magore/allsky-rpi-hq-camera-enclosure/images/BOTTOM-COVER-AND-WEATHER-SENSOR/ALLSKY-CAMERA-BOTTOM-VIEW-CLOSEUP.jpg

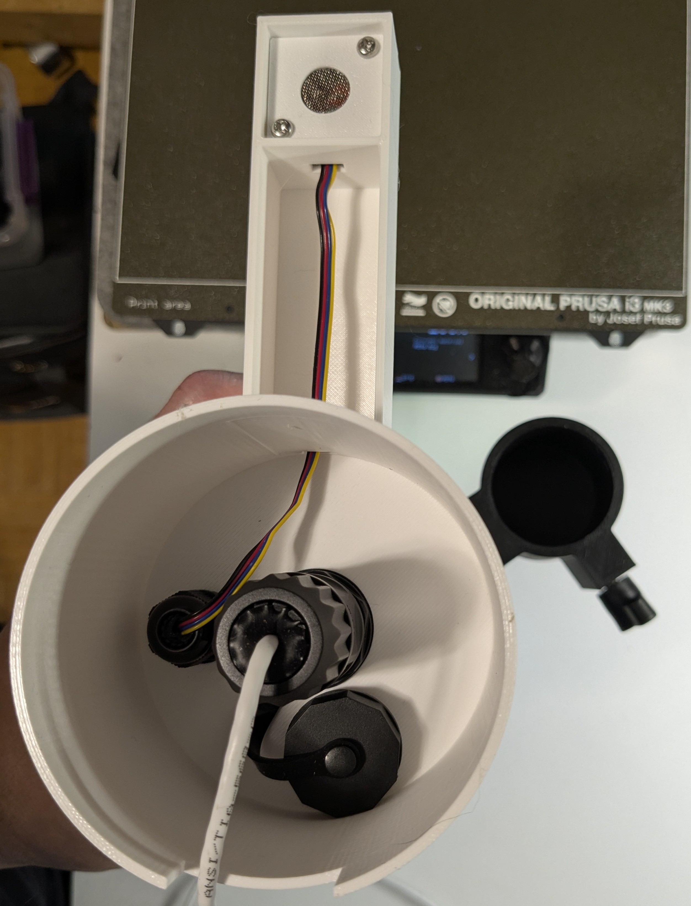
images/BOTTOM-COVER-AND-WEATHER-SENSOR/ALLSKY-CAMERA-BOTTOM-VIEW-CLOSEUP.jpg
