magore/allsky-rpi-hq-camera-enclosure/images/BOTTOM-COVER-AND-WEATHER-SENSOR/WEATHER-SENSOR-AND-COVER.jpg

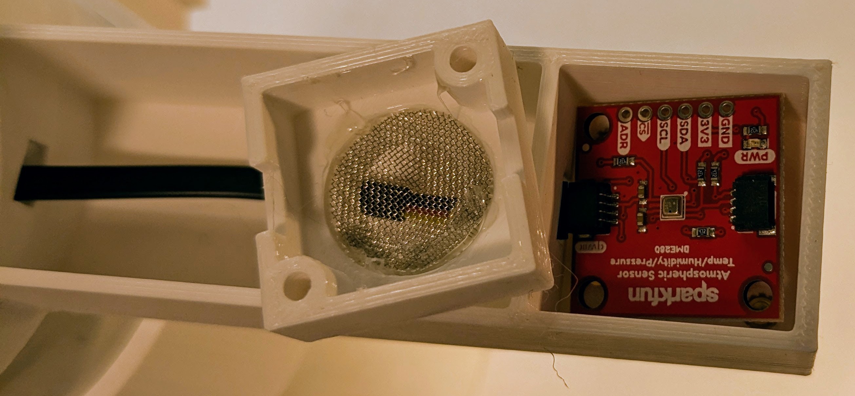
images/BOTTOM-COVER-AND-WEATHER-SENSOR/WEATHER-SENSOR-AND-COVER.jpg
