magore/allsky-rpi-hq-camera-enclosure/images/BOTTOM-COVER-AND-WEATHER-SENSOR/WEATHER-SENSOR-COVER-AND-SCREEN.jpg

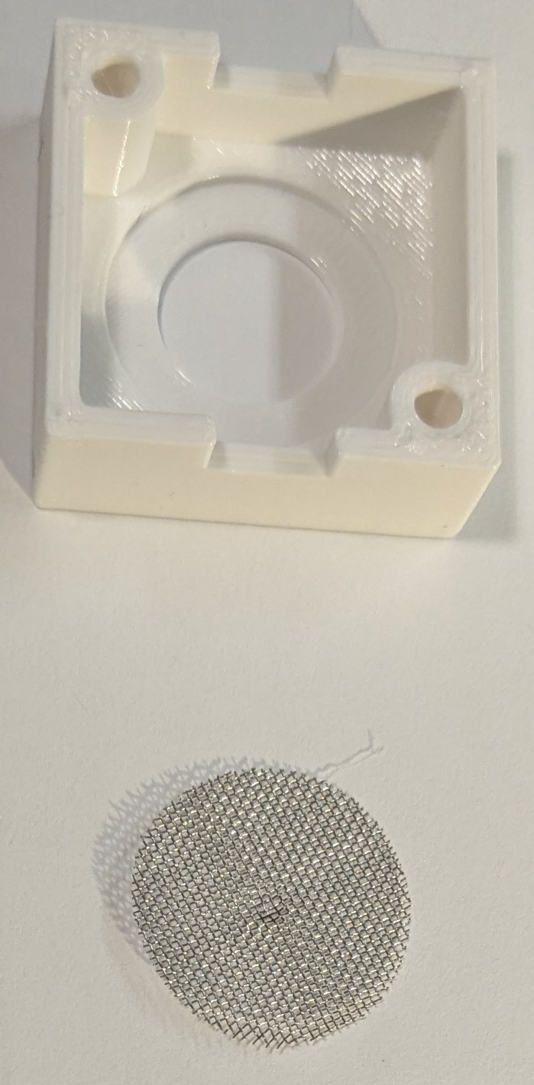
images/BOTTOM-COVER-AND-WEATHER-SENSOR/WEATHER-SENSOR-COVER-AND-SCREEN.jpg
