magore/allsky-rpi-hq-camera-enclosure/images/enclosure.jpg

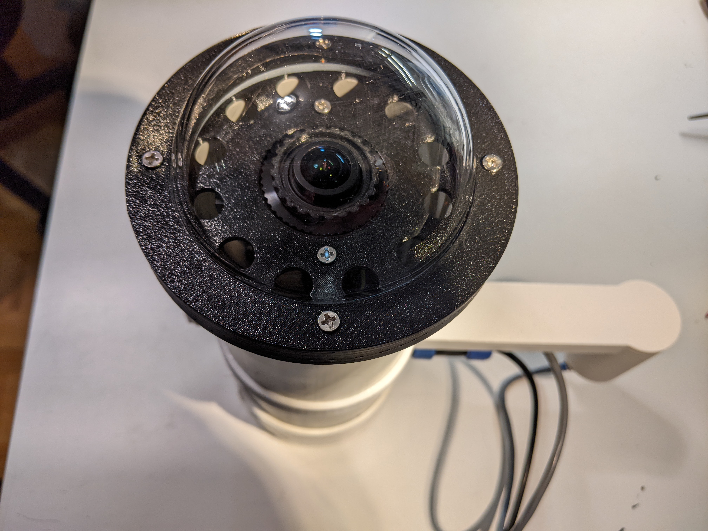
images/enclosure.jpg
