magore/allsky-rpi-hq-camera-enclosure/images/HEAT-SET-INSERT-INSTALLATION/HEAT-SET-INSERT-REQUIRMENTS-FOR-THIS-PROJECTS-CAD-DESIGN.jpg

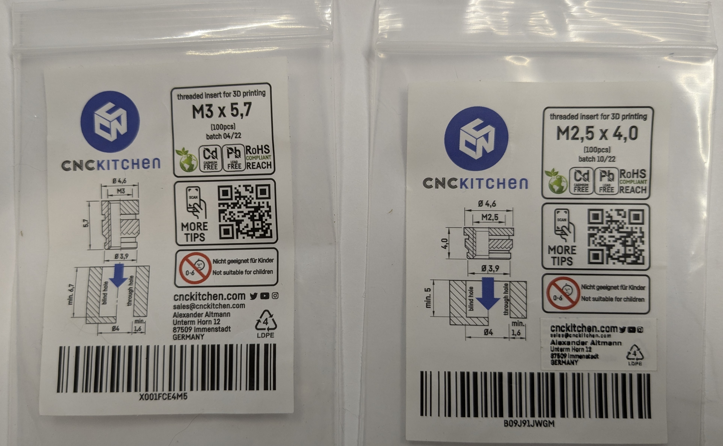
images/HEAT-SET-INSERT-INSTALLATION/HEAT-SET-INSERT-REQUIRMENTS-FOR-THIS-PROJECTS-CAD-DESIGN.jpg
