magore/allsky-rpi-hq-camera-enclosure/images/MAGNETIC-FOCUS/MAGNETIC-FOCUS-ADJUSTMENT.jpg

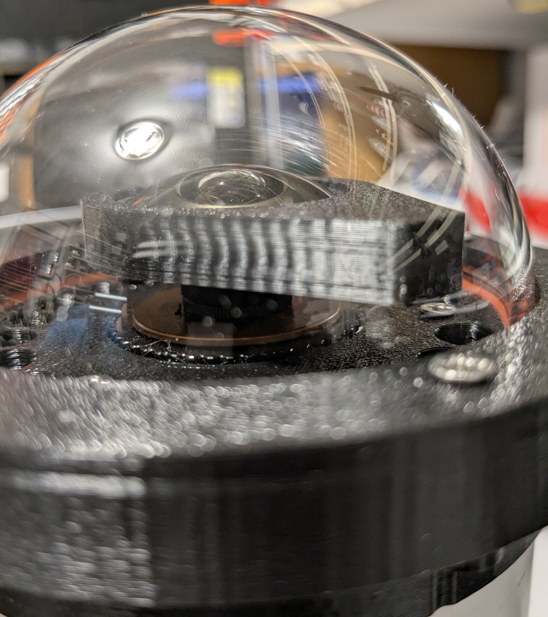
images/MAGNETIC-FOCUS/MAGNETIC-FOCUS-ADJUSTMENT.jpg
