magore/allsky-rpi-hq-camera-enclosure/images/MOUNTING/ALLSKY-POLLTOP-MOUNT-ADAPTER.jpg

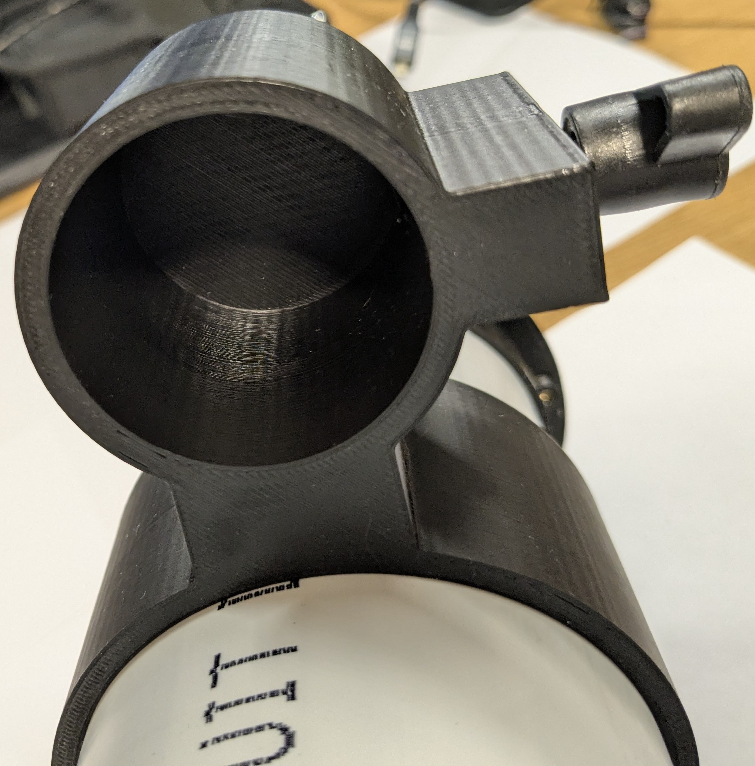
images/MOUNTING/ALLSKY-POLLTOP-MOUNT-ADAPTER.jpg
