magore/allsky-rpi-hq-camera-enclosure/images/O-RING-INSTALLATION/ALLSKY-CAMERA-O-RING-VERSION-OPTICAL-COVER-REMOVED.jpg

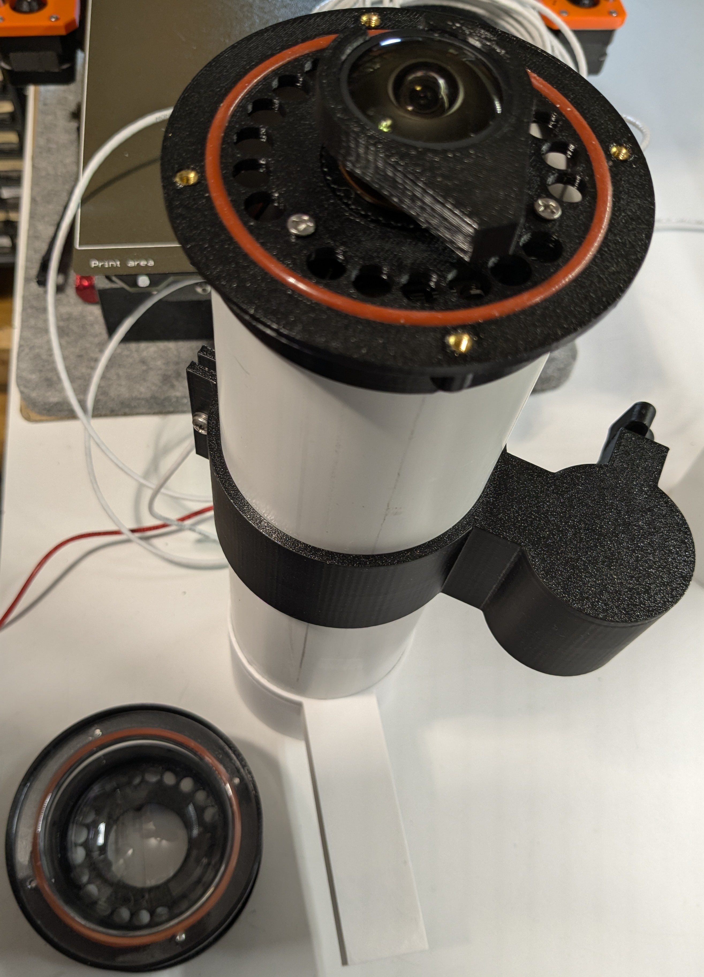
images/O-RING-INSTALLATION/ALLSKY-CAMERA-O-RING-VERSION-OPTICAL-COVER-REMOVED.jpg
