magore/allsky-rpi-hq-camera-enclosure/images/O-RING-INSTALLATION/TOP-COVER-OPTICAL-DOME-O-RINGs.jpg

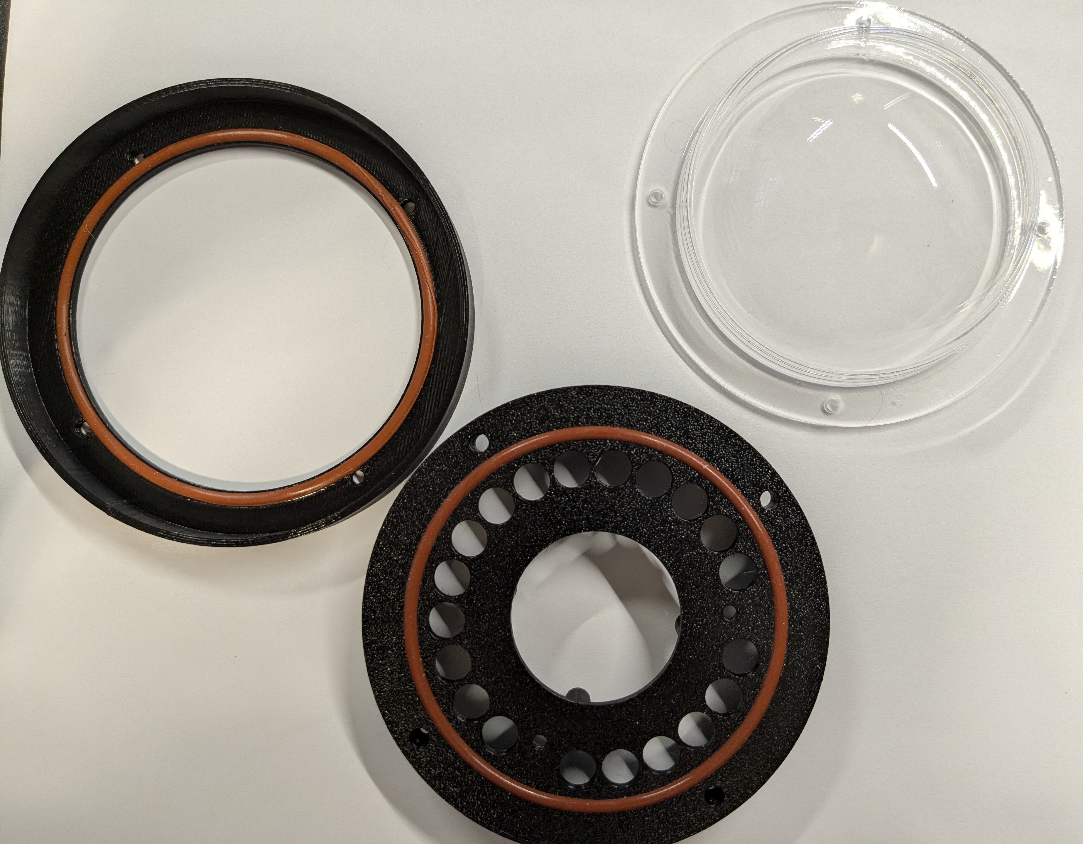
images/O-RING-INSTALLATION/TOP-COVER-OPTICAL-DOME-O-RINGs.jpg
