magore/allsky-rpi-hq-camera-enclosure/images/WEATHER-SENSOR-AND-BOTTOP-COVER-TOP-INSIDE-VIEW.jpg

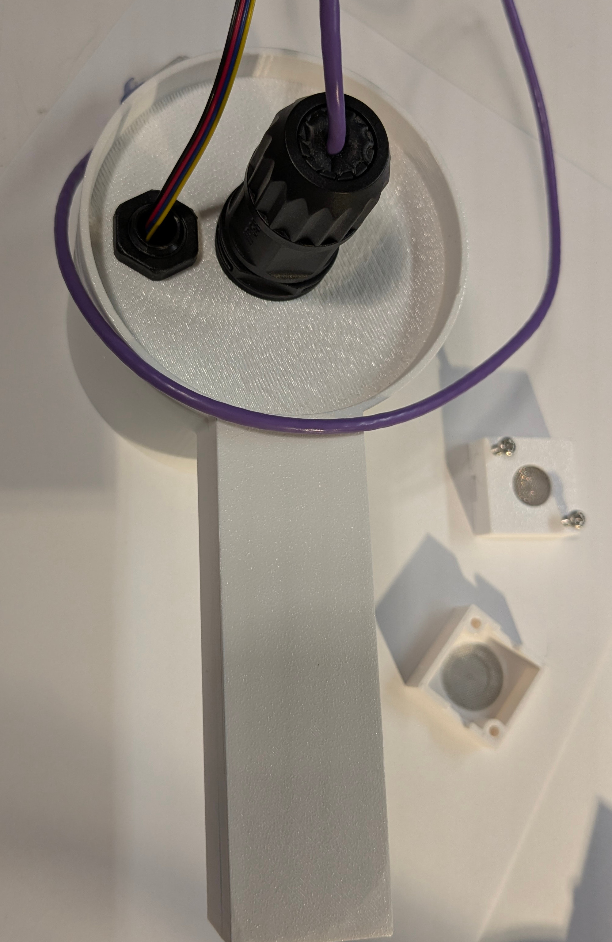
images/WEATHER-SENSOR-AND-BOTTOP-COVER-TOP-INSIDE-VIEW.jpg
