magore/allsky-rpi-hq-camera-enclosure/images/BOTTOM-COVER-AND-WEATHER-SENSOR/BOTTOM-VIEW-WEATHER-SENSOR-INSIDE-ASSEMBLY-VIEW.jpg

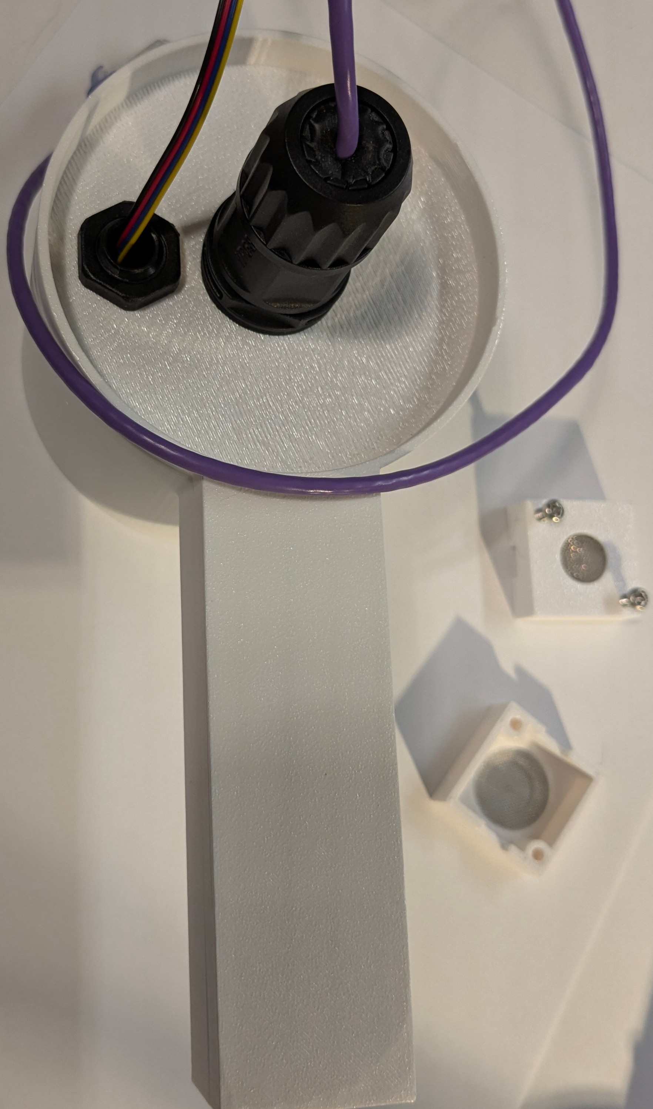
images/BOTTOM-COVER-AND-WEATHER-SENSOR/BOTTOM-VIEW-WEATHER-SENSOR-INSIDE-ASSEMBLY-VIEW.jpg
