magore/allsky-rpi-hq-camera-enclosure/images/HEAT-SET-INSERT-INSTALLATION/HOWTO-INSTALL--HEAT-SET-INSERTS.jpg

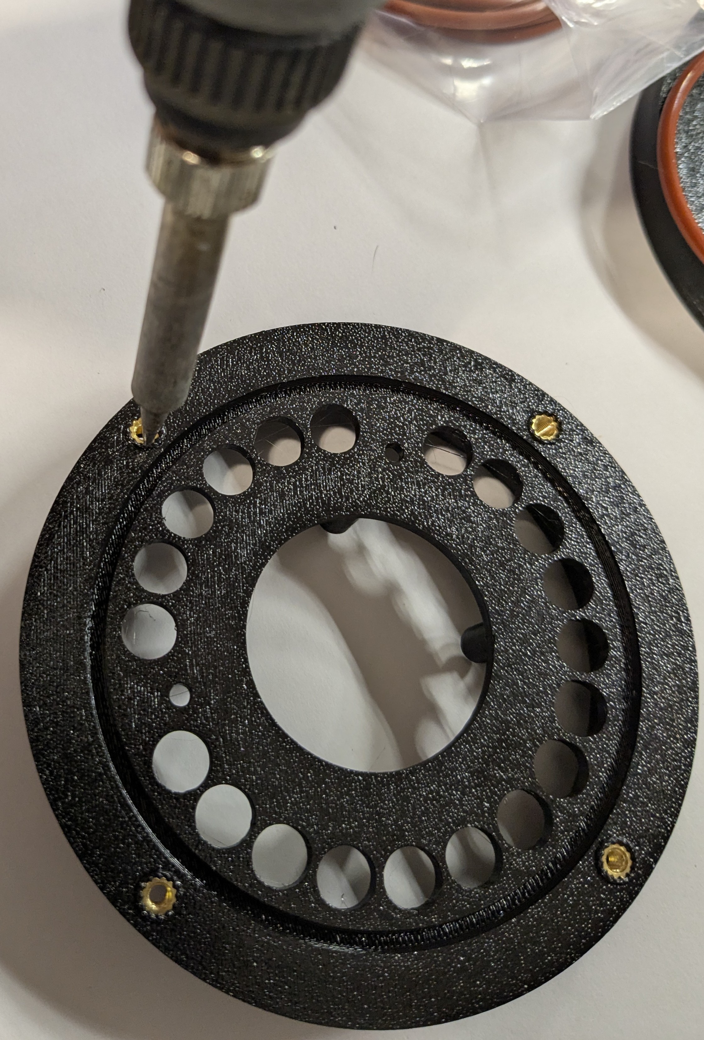
images/HEAT-SET-INSERT-INSTALLATION/HOWTO-INSTALL--HEAT-SET-INSERTS.jpg
