magore/allsky-rpi-hq-camera-enclosure/images/HEAT-SET-INSERT-INSTALLATION/SOLDERING-IRON-TIP-AND-INSERTS.jpg

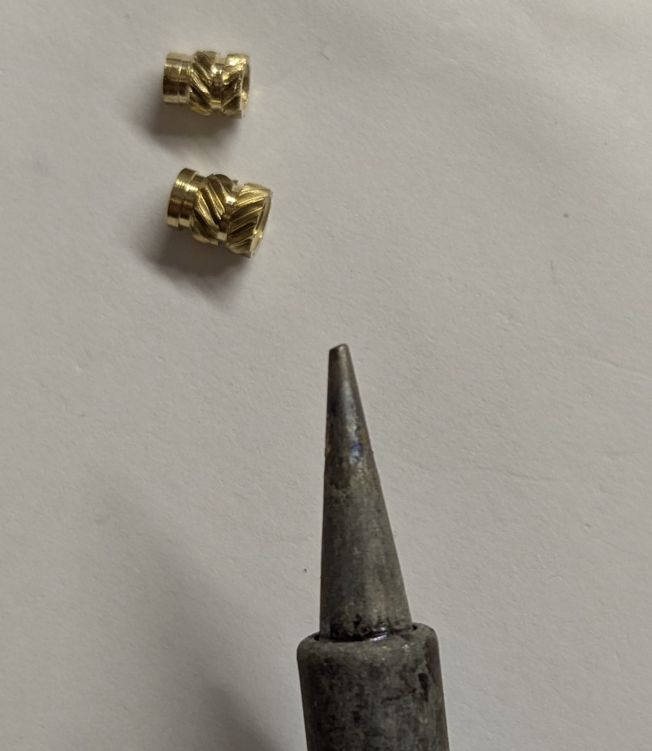
images/HEAT-SET-INSERT-INSTALLATION/SOLDERING-IRON-TIP-AND-INSERTS.jpg
