magore/allsky-rpi-hq-camera-enclosure/images/HEAT-SET-INSERT-INSTALLATION/TOP-ASSEMBLY-CAMERA-HEAT-SET-INSERTS-BEFORE-INSERTION.jpg

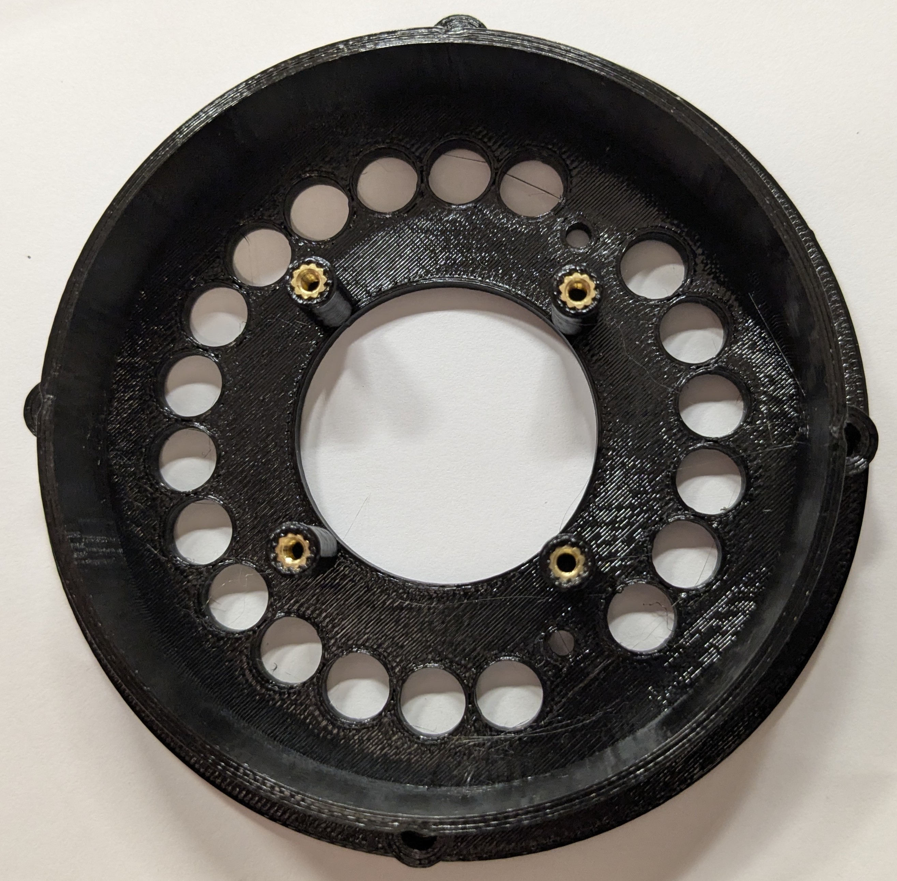
images/HEAT-SET-INSERT-INSTALLATION/TOP-ASSEMBLY-CAMERA-HEAT-SET-INSERTS-BEFORE-INSERTION.jpg
