magore/allsky-rpi-hq-camera-enclosure/images/HEAT-SET-INSERT-INSTALLATION/TOP-ASSEMBLY-CAMERA-SIDE-HEAT-SET-INSERTS-AFTER-INSERTION.jpg

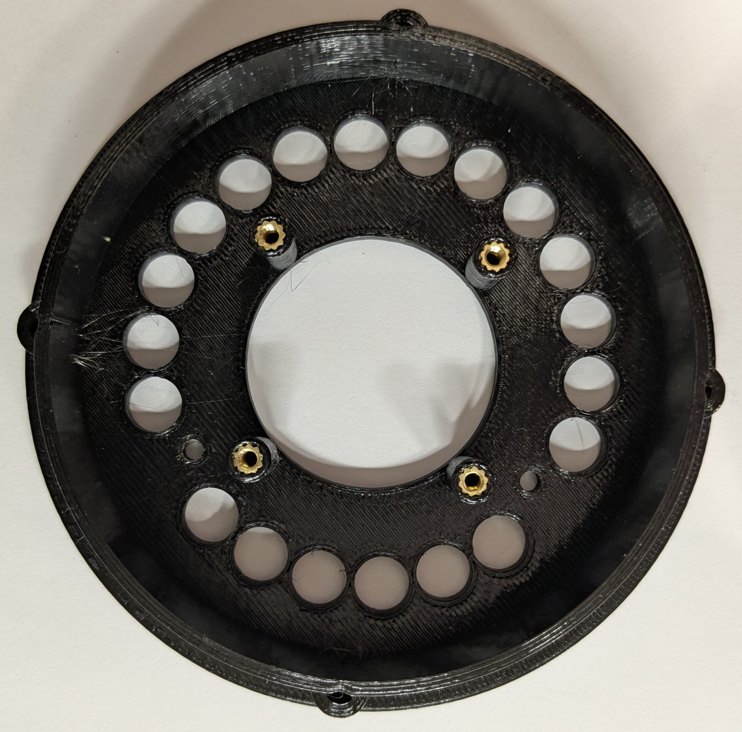
images/HEAT-SET-INSERT-INSTALLATION/TOP-ASSEMBLY-CAMERA-SIDE-HEAT-SET-INSERTS-AFTER-INSERTION.jpg
