magore/allsky-rpi-hq-camera-enclosure/images/HEAT-SET-INSERT-INSTALLATION/TOP-ASSEMBLY-WITH-SUPPORT-NO-RPI.jpg

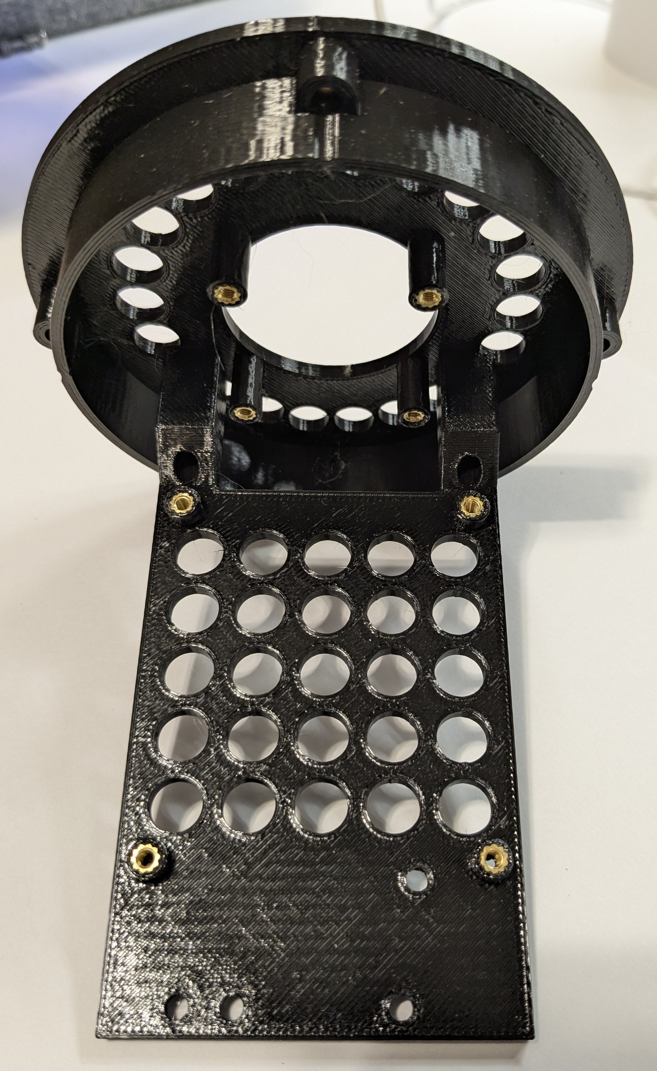
images/HEAT-SET-INSERT-INSTALLATION/TOP-ASSEMBLY-WITH-SUPPORT-NO-RPI.jpg
