magore/allsky-rpi-hq-camera-enclosure/images/O-RING-INSTALLATION/TOP-ASSEMBLY-O-RING-INSTALLATION.jpg

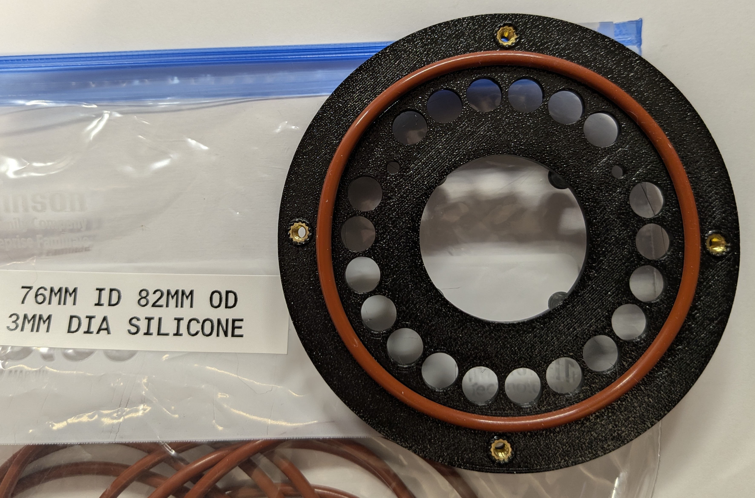
images/O-RING-INSTALLATION/TOP-ASSEMBLY-O-RING-INSTALLATION.jpg
