magore/allsky-rpi-hq-camera-enclosure/images/O-RING-INSTALLATION/TOP-ASSEMBLY-REMOVING-3D-PRINTER-SUPPORTS-FOR-O-RING.jpg

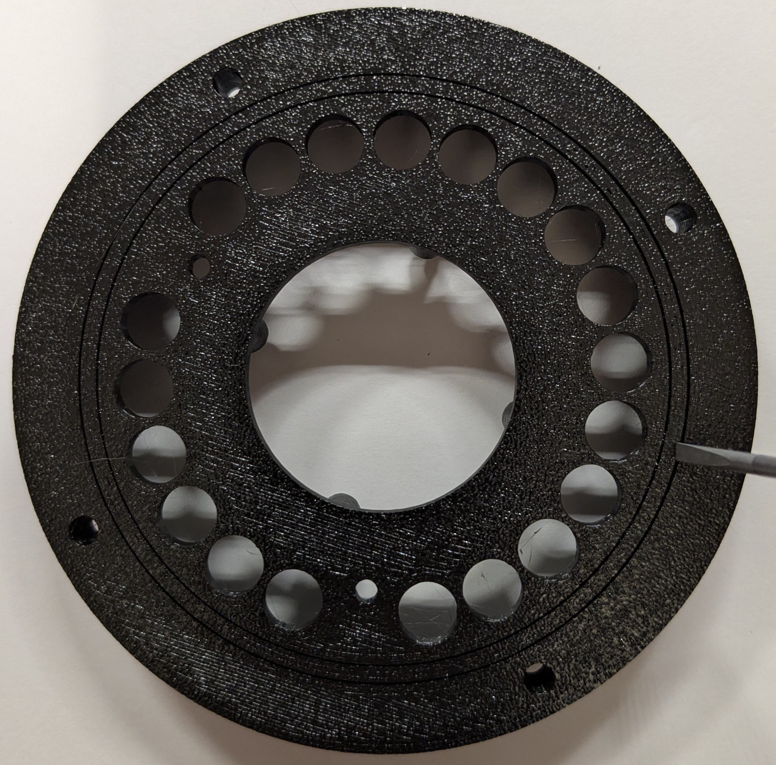
images/O-RING-INSTALLATION/TOP-ASSEMBLY-REMOVING-3D-PRINTER-SUPPORTS-FOR-O-RING.jpg
