magore/allsky-rpi-hq-camera-enclosure/images/O-RING-INSTALLATION/TOP-COVER-O-RING-AND-DOME-INSTALLED.jpg

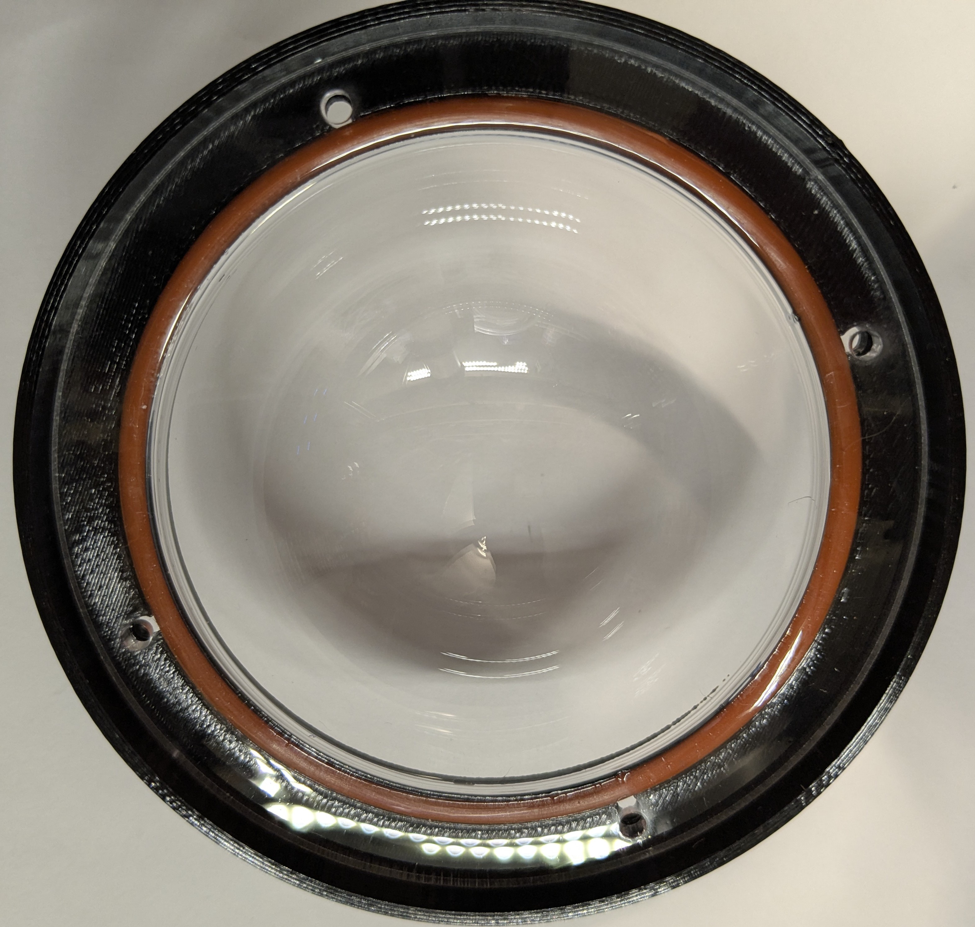
images/O-RING-INSTALLATION/TOP-COVER-O-RING-AND-DOME-INSTALLED.jpg
