magore/allsky-rpi-hq-camera-enclosure/images/O-RING-INSTALLATION/TOP-COVER-O-RING-INSTALLED.jpg

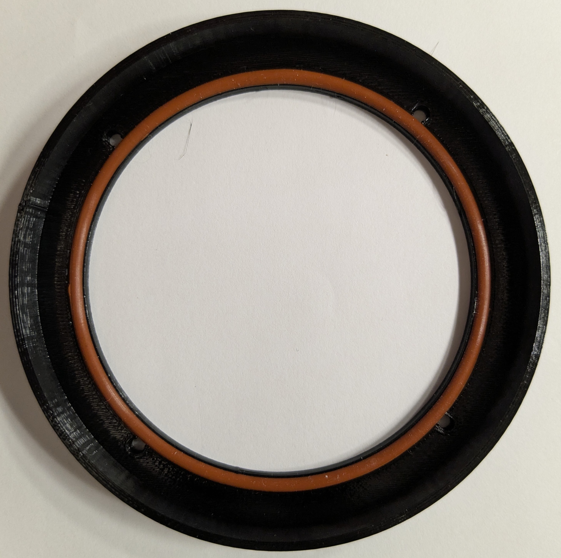
images/O-RING-INSTALLATION/TOP-COVER-O-RING-INSTALLED.jpg
