magore/allsky-rpi-hq-camera-enclosure/images/RPI-INSTALLATION/BOTTOM-VIEW-OF-RASPBERRY-PI-5-BATTERY.jpg

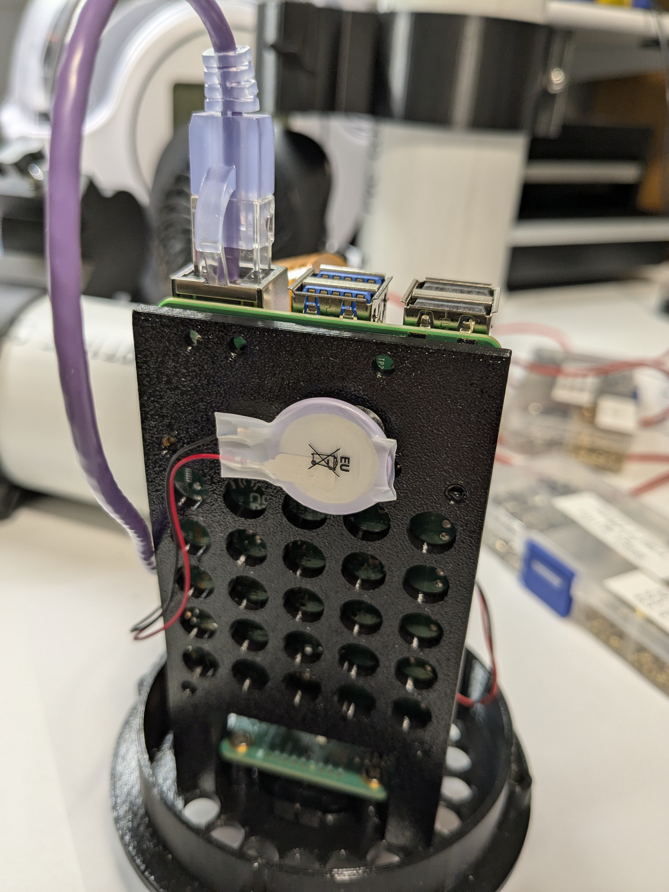
images/RPI-INSTALLATION/BOTTOM-VIEW-OF-RASPBERRY-PI-5-BATTERY.jpg
