magore/allsky-rpi-hq-camera-enclosure/images/RPI-INSTALLATION/Hacker-Gadgets-Raspberry-Pi-5-PoE-and-NVME-HAT.jpg

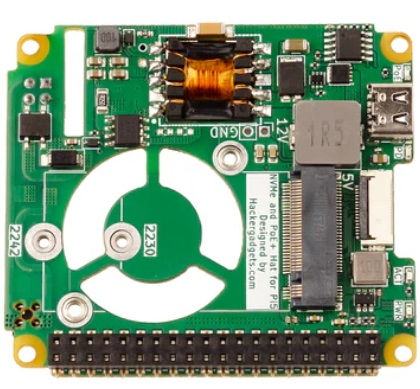
images/RPI-INSTALLATION/Hacker-Gadgets-Raspberry-Pi-5-PoE-and-NVME-HAT.jpg
