magore/allsky-rpi-hq-camera-enclosure/images/RPI-INSTALLATION/SIDE-VIEW-OF-RASPBERRY-PI-5-SHOWING-HEADER-EXTENSION.jpg

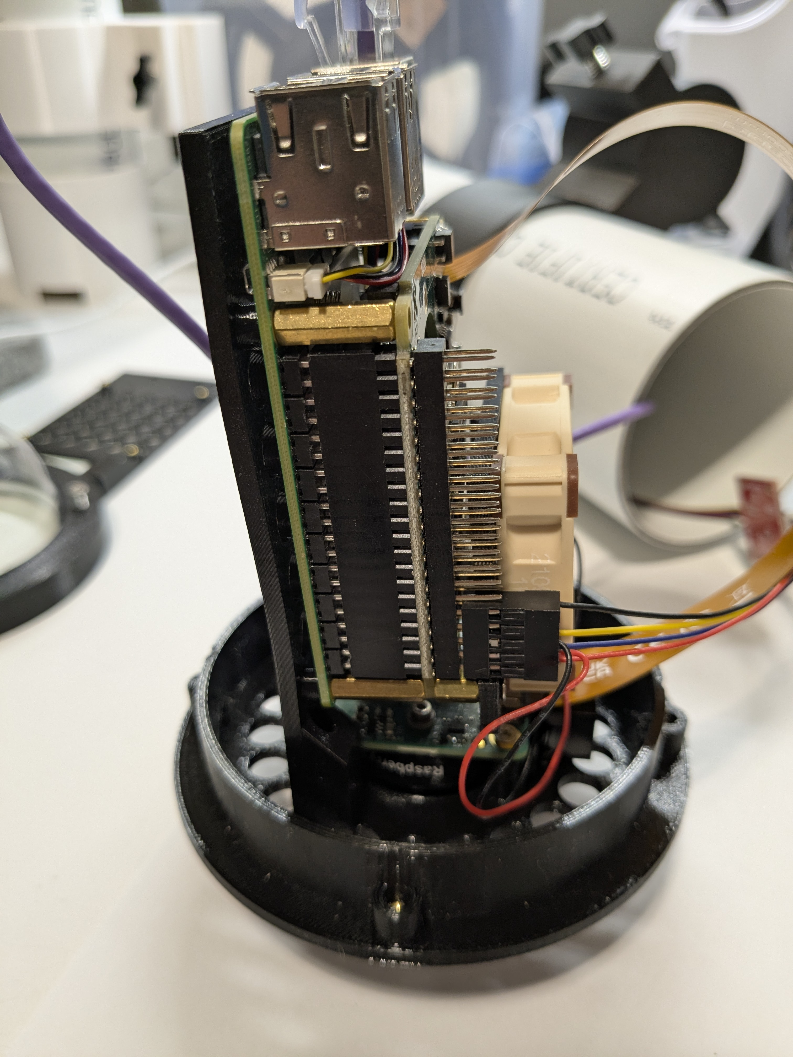
images/RPI-INSTALLATION/SIDE-VIEW-OF-RASPBERRY-PI-5-SHOWING-HEADER-EXTENSION.jpg
