magore/allsky-rpi-hq-camera-enclosure/images/RPI-INSTALLATION/SIDE-VIEW-OF-RASPBERRY-PI-5-WITH-CAMERA-ASSEMBLY.jpg

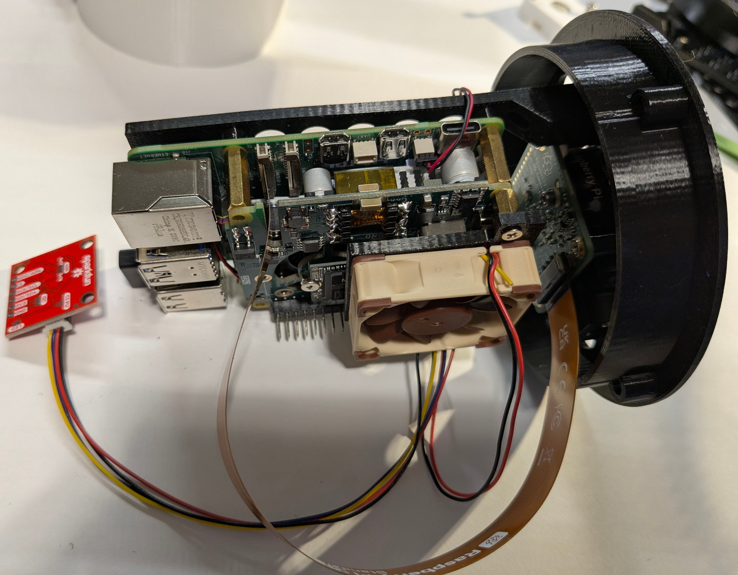
images/RPI-INSTALLATION/SIDE-VIEW-OF-RASPBERRY-PI-5-WITH-CAMERA-ASSEMBLY.jpg
