magore/allsky-rpi-hq-camera-enclosure/images/RPI-INSTALLATION/TOP-VIEW-OF-RASPBERRY-PI-4-WITHOUT-FAN-SHOWING-WIRING.jpg

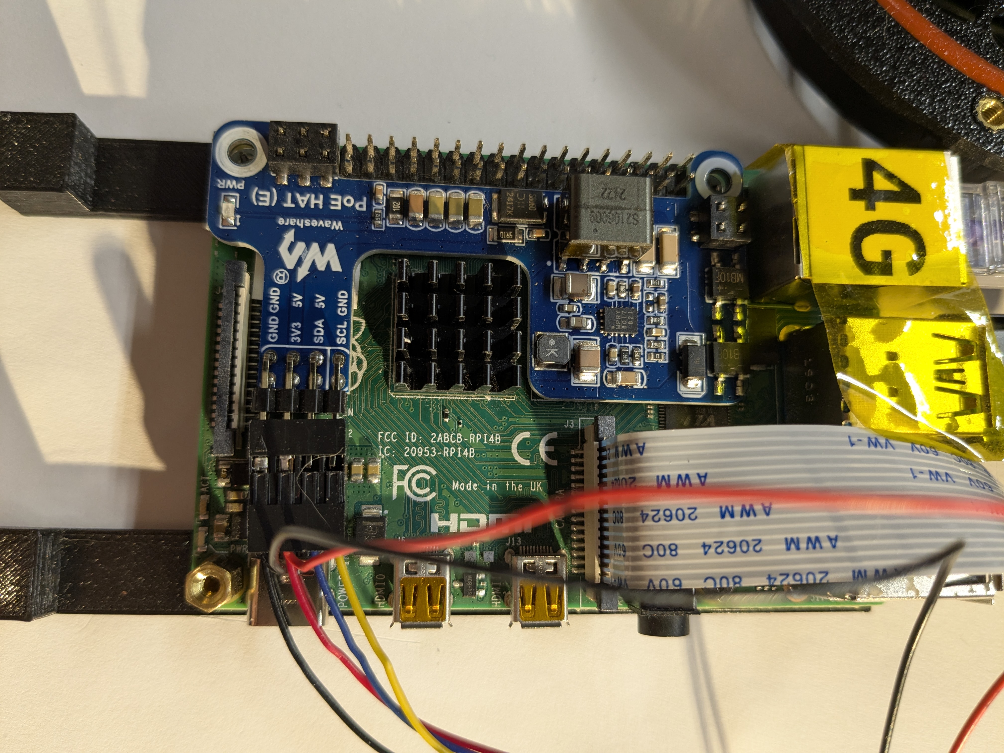
images/RPI-INSTALLATION/TOP-VIEW-OF-RASPBERRY-PI-4-WITHOUT-FAN-SHOWING-WIRING.jpg
