magore/allsky-rpi-hq-camera-enclosure/images/RPI-INSTALLATION/TOP-VIEW-OF-RASPBERRY-PI-5-WITH-CAMERA-ASSEMBLY.jpg

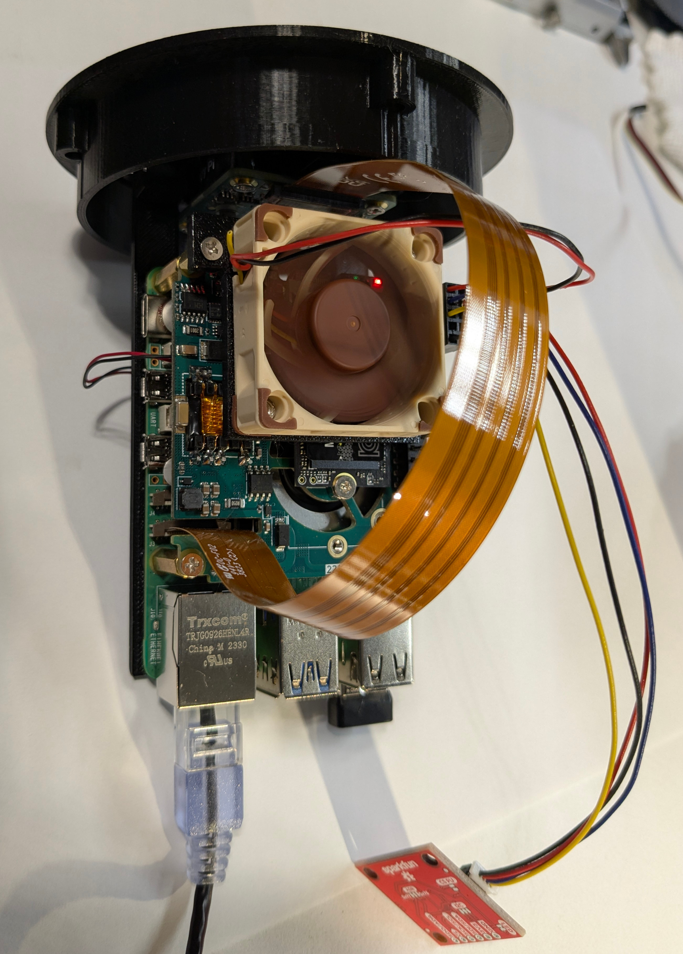
images/RPI-INSTALLATION/TOP-VIEW-OF-RASPBERRY-PI-5-WITH-CAMERA-ASSEMBLY.jpg
