magore/allsky-rpi-hq-camera-enclosure/images/RPI-INSTALLATION/Waveshare-PoE-HAT-version-E-for-Raspberry-Pi-4.jpg

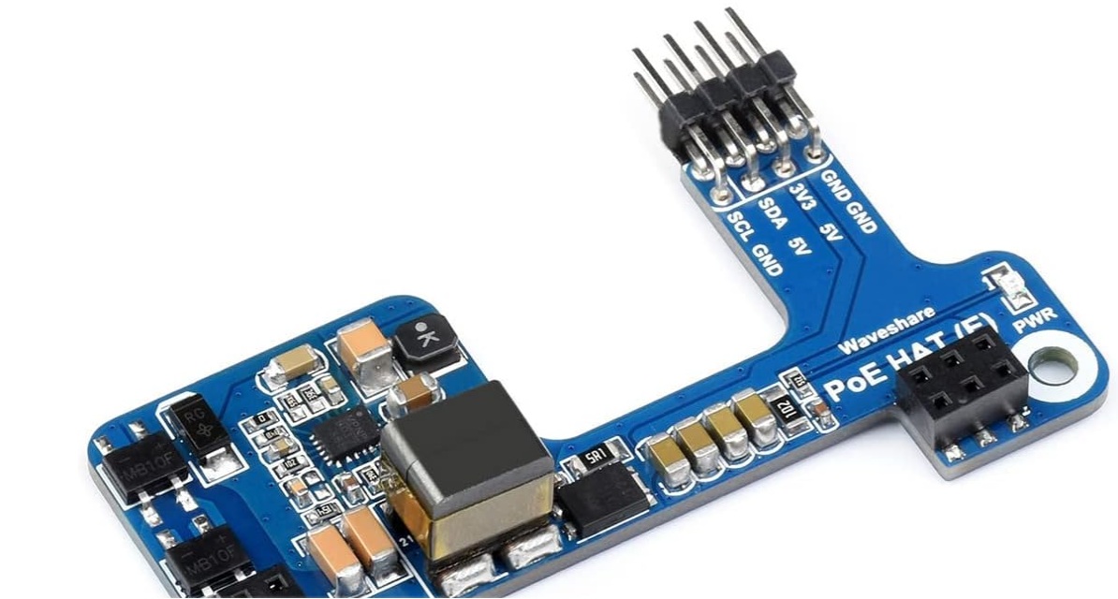
images/RPI-INSTALLATION/Waveshare-PoE-HAT-version-E-for-Raspberry-Pi-4.jpg
